Phayuth/delivery_robot/dlvr_resource/design/Part/Voltage_Display.SLDPRT

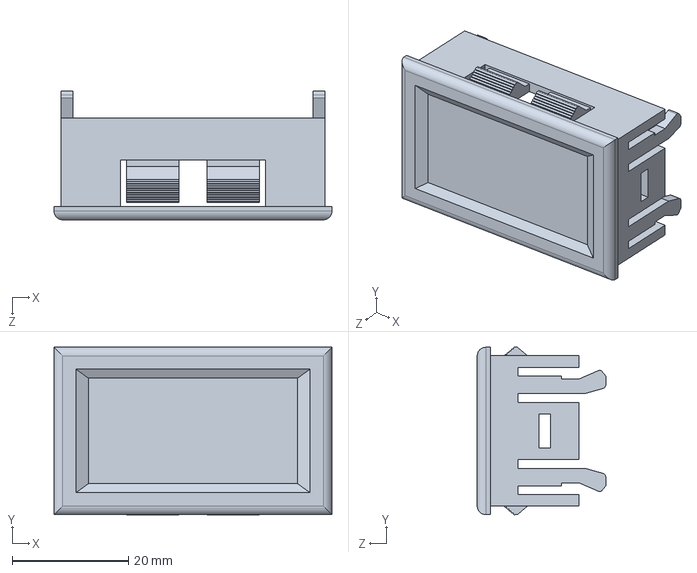
[picture p19: CAD file, 2022-11-23]
dlvr_resource/design/Part/Voltage_Display.SLDPRT
47.8 x 28.8 x 22.1 mm
