Phayuth/delivery_robot/dlvr_robot_description/meshes/laser_link.STL

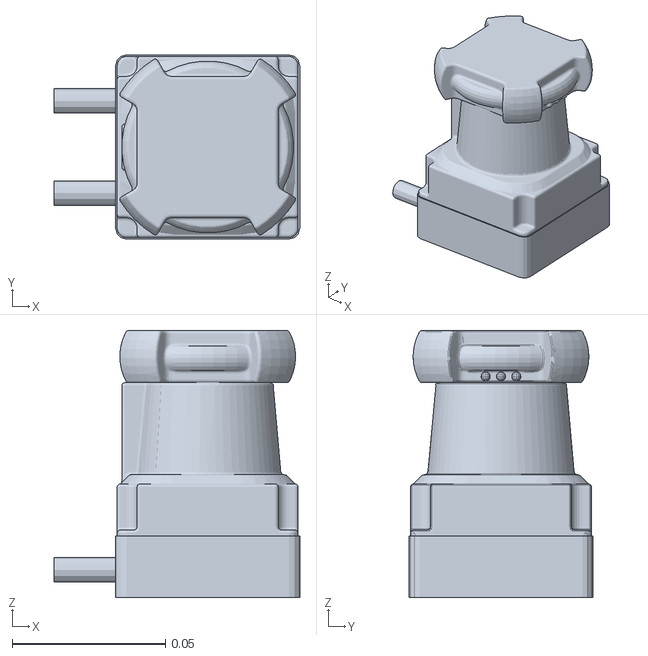
[picture p20: CAD file, 2022-11-23]
dlvr_robot_description/meshes/laser_link.STL
0.08 x 0.06 x 0.087
