Phayuth/delivery_robot/dlvr_resource/design/Part/Structure.SLDPRT

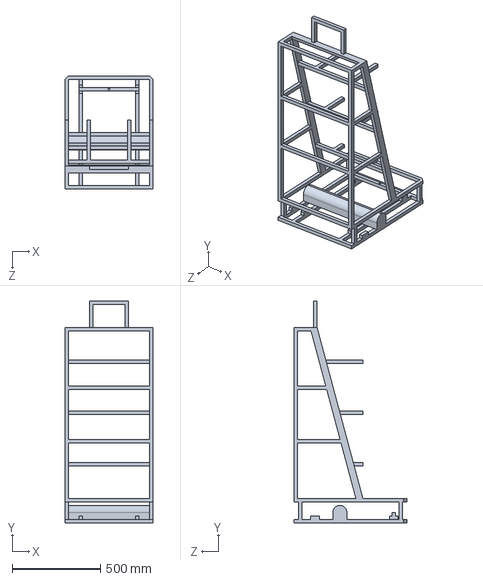
[picture p21: CAD file, 2022-11-23]
dlvr_resource/design/Part/Structure.SLDPRT
500.0 x 1255.9 x 640.0 mm
