Phayuth/delivery_robot/dlvr_resource/design/Part/Plate.SLDPRT

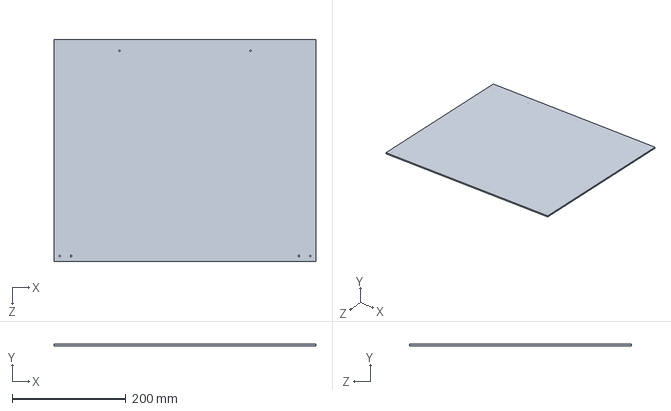
[picture p22: CAD file, 2022-11-23]
dlvr_resource/design/Part/Plate.SLDPRT
460.0 x 3.00 x 390.5 mm
