Phayuth/delivery_robot/dlvr_resource/design/Part/Top_Back_Cover_1.SLDPRT

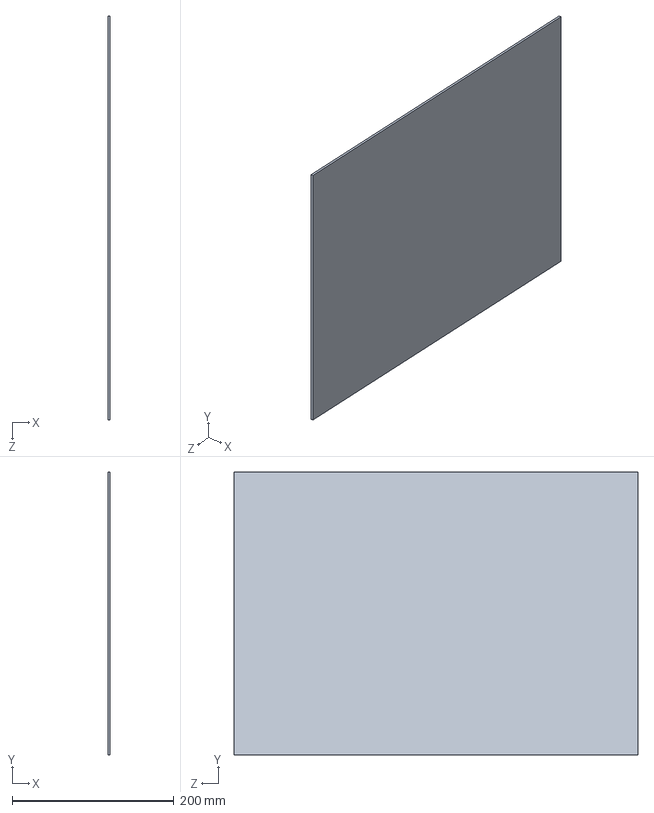
[picture p23: CAD file, 2022-11-23]
dlvr_resource/design/Part/Top_Back_Cover_1.SLDPRT
3.00 x 350.4 x 500.0 mm
