Phayuth/delivery_robot/dlvr_resource/design/Part/System_Controller_Support.SLDPRT

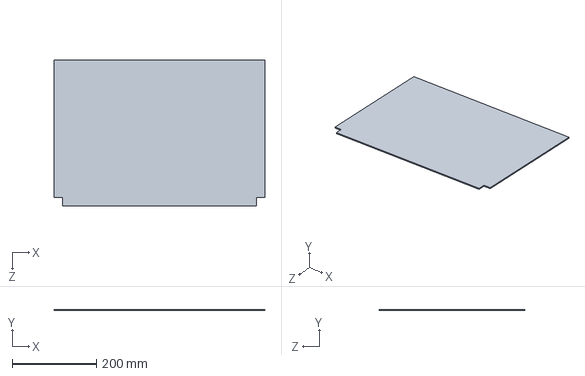
[picture p24: CAD file, 2022-11-23]
dlvr_resource/design/Part/System_Controller_Support.SLDPRT
500.0 x 3.00 x 345.0 mm
