Phayuth/delivery_robot/dlvr_resource/design/Part/Top_Side_Cover_2.SLDPRT

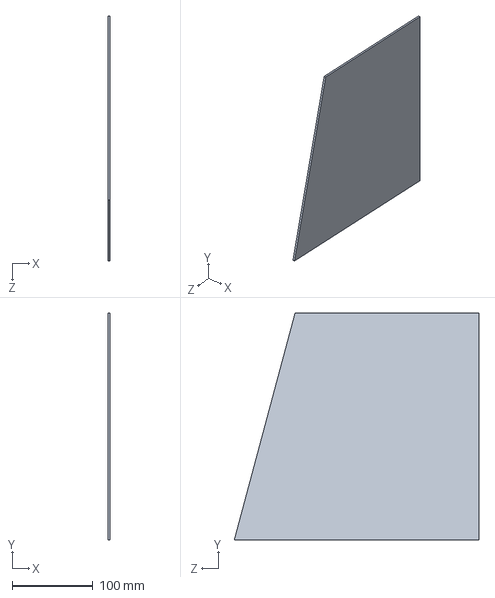
[picture p25: CAD file, 2022-11-23]
dlvr_resource/design/Part/Top_Side_Cover_2.SLDPRT
3.00 x 281.9 x 303.6 mm
