Phayuth/delivery_robot/dlvr_resource/design/Part/E_Stop_Button.SLDPRT

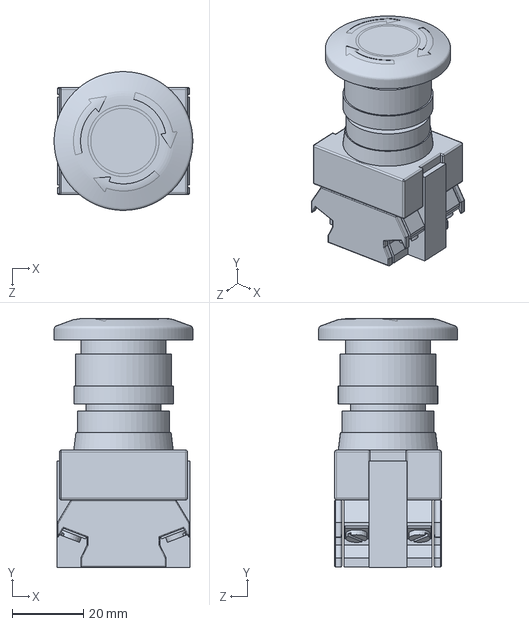
[picture p26: CAD file, 2022-11-23]
dlvr_resource/design/Part/E_Stop_Button.SLDPRT
39.0 x 70.0 x 39.0 mm
