Phayuth/delivery_robot/dlvr_resource/design/Part/Bottom_Angle_Cover_1.SLDPRT

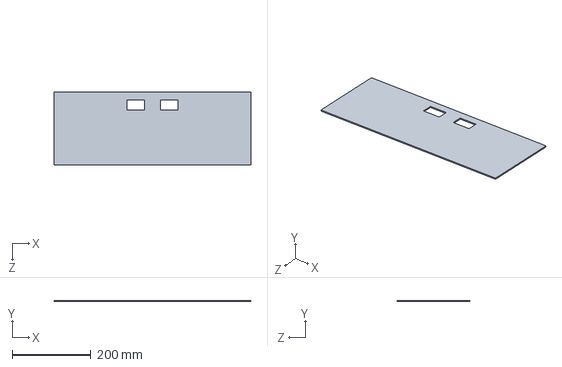
[picture p27: CAD file, 2022-11-23]
dlvr_resource/design/Part/Bottom_Angle_Cover_1.SLDPRT
500.0 x 3.00 x 185.0 mm
