Phayuth/delivery_robot/dlvr_resource/design/Part/AC_Power_Socket.SLDPRT

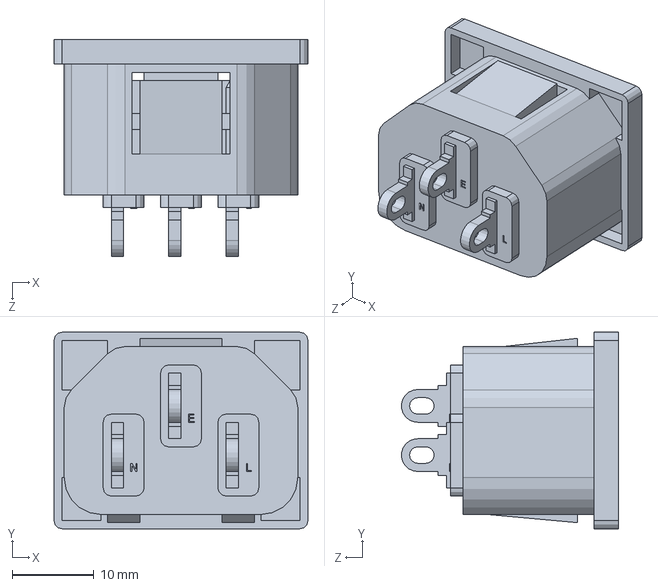
[picture p28: CAD file, 2022-11-23]
dlvr_resource/design/Part/AC_Power_Socket.SLDPRT
31.0 x 24.0 x 26.5 mm
