Phayuth/delivery_robot/dlvr_resource/design/Part/Bottom_Side_Cover.SLDPRT

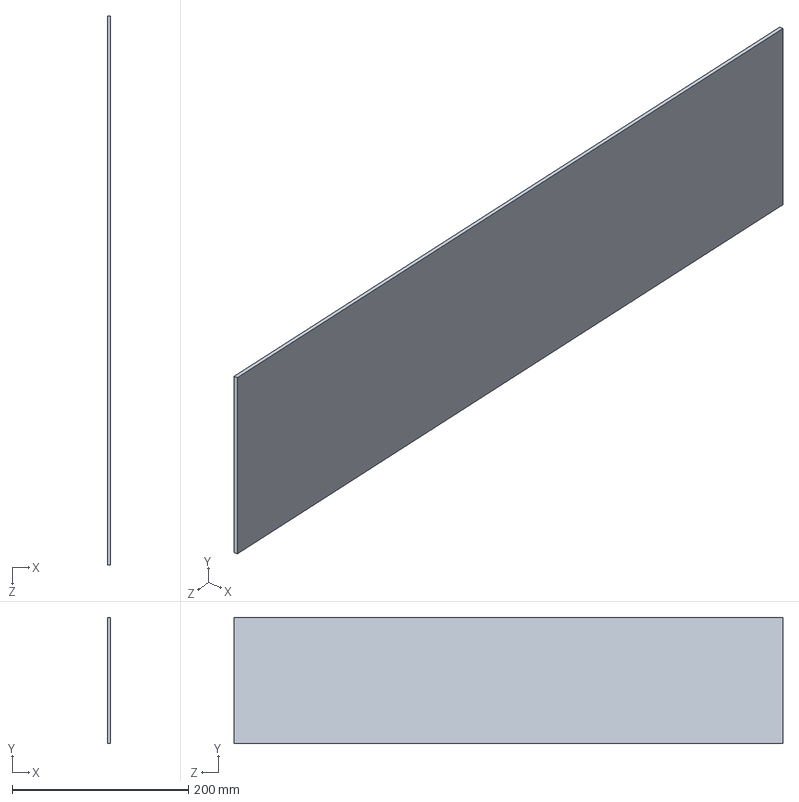
[picture p29: CAD file, 2022-11-23]
dlvr_resource/design/Part/Bottom_Side_Cover.SLDPRT
3.00 x 143.0 x 623.0 mm
