Phayuth/delivery_robot/dlvr_resource/design/Part/LCD_Support.SLDPRT

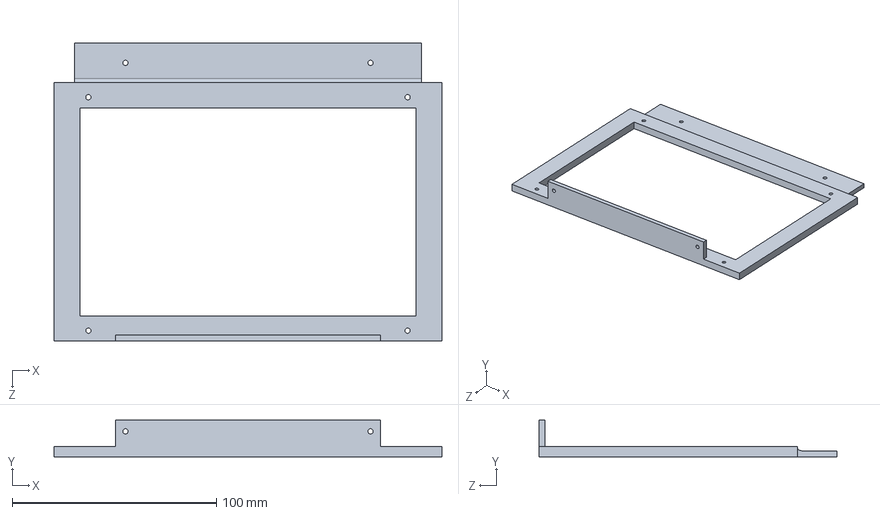
[picture p30: CAD file, 2022-11-23]
dlvr_resource/design/Part/LCD_Support.SLDPRT
190.0 x 18.0 x 146.0 mm
