Phayuth/delivery_robot/dlvr_resource/design/Part/Bottom_Front_Cover.SLDPRT

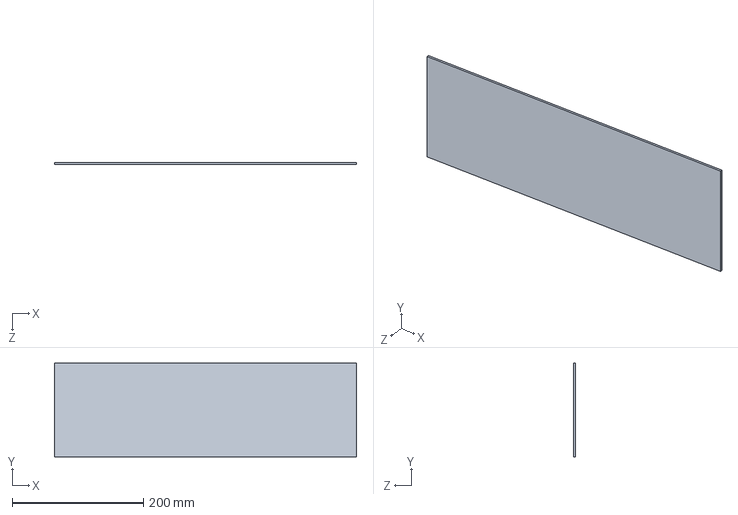
[picture p31: CAD file, 2022-11-23]
dlvr_resource/design/Part/Bottom_Front_Cover.SLDPRT
460.0 x 143.0 x 3.00 mm
