Phayuth/delivery_robot/dlvr_resource/design/Part/Logitech_C920.SLDPRT

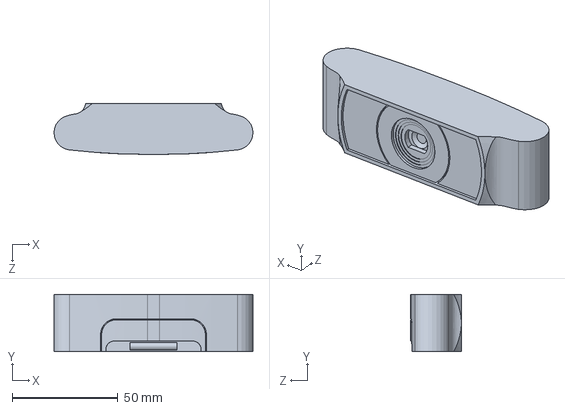
[picture p32: CAD file, 2022-11-23]
dlvr_resource/design/Part/Logitech_C920.SLDPRT
94.0 x 27.0 x 24.0 mm
