Phayuth/delivery_robot/dlvr_resource/design/Part/Top_Top_Cover.SLDPRT

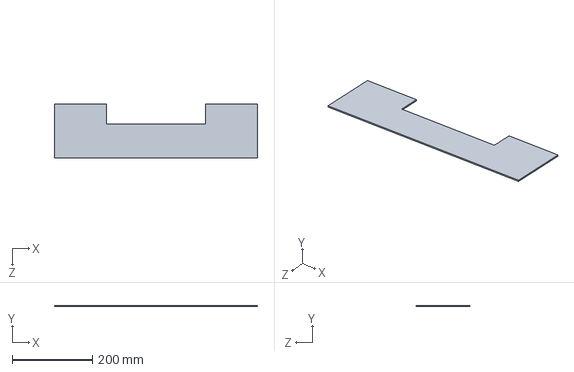
[picture p33: CAD file, 2022-11-23]
dlvr_resource/design/Part/Top_Top_Cover.SLDPRT
506.0 x 3.00 x 134.2 mm
