Phayuth/delivery_robot/dlvr_resource/design/Part/System_Monitor_Support.SLDPRT

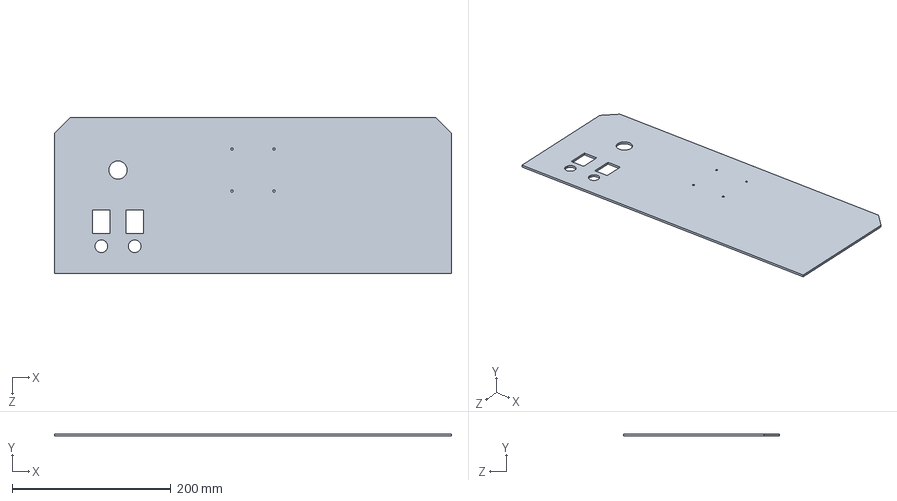
[picture p34: CAD file, 2022-11-23]
dlvr_resource/design/Part/System_Monitor_Support.SLDPRT
500.0 x 3.00 x 197.1 mm
