Phayuth/delivery_robot/dlvr_resource/design/Part/LIDAR_Hokuyo_UTM_30LX.SLDPRT

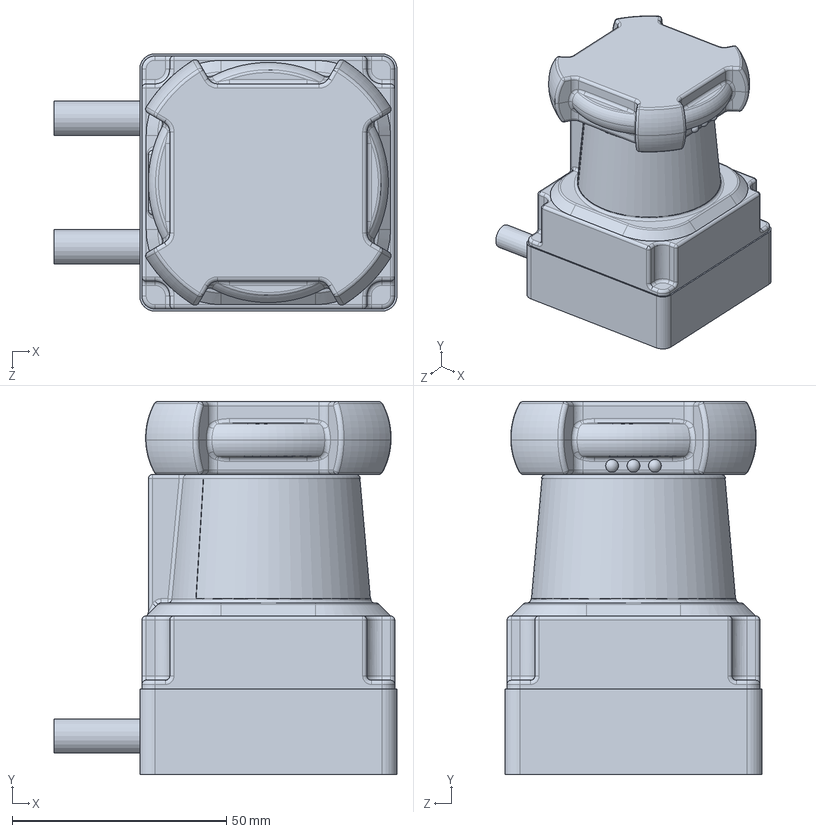
[picture p36: CAD file, 2022-11-23]
dlvr_resource/design/Part/LIDAR_Hokuyo_UTM_30LX.SLDPRT
80.0 x 87.0 x 60.0 mm
