Phayuth/delivery_robot/dlvr_resource/design/Part/Bottom_Chamfer_Cover.SLDPRT

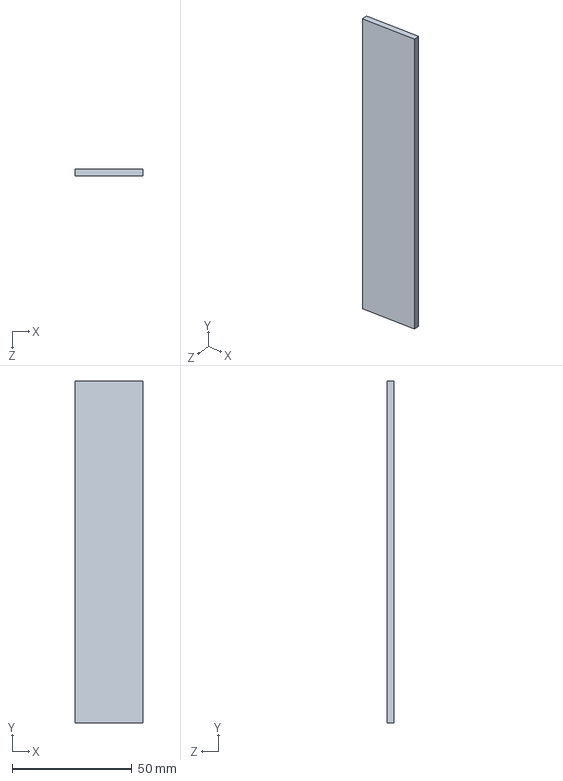
[picture p37: CAD file, 2022-11-23]
dlvr_resource/design/Part/Bottom_Chamfer_Cover.SLDPRT
28.3 x 143.0 x 3.00 mm
