Phayuth/delivery_robot/dlvr_resource/design/Part/Battery_Switch.SLDPRT

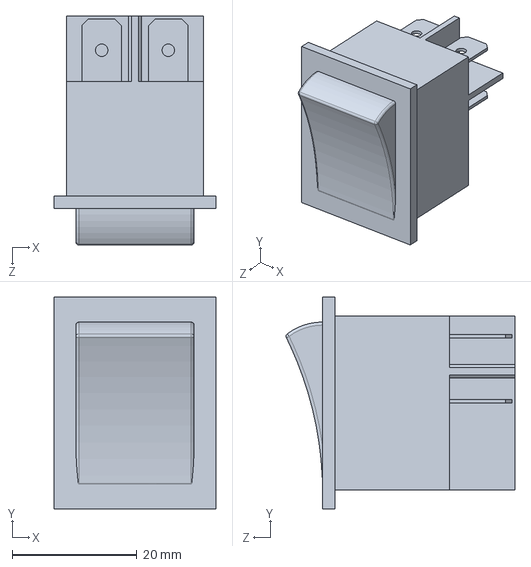
[picture p38: CAD file, 2022-11-23]
dlvr_resource/design/Part/Battery_Switch.SLDPRT
26.0 x 34.0 x 36.8 mm
