Phayuth/delivery_robot/dlvr_resource/design/Part/Bottom_Battery_Support_2.SLDPRT

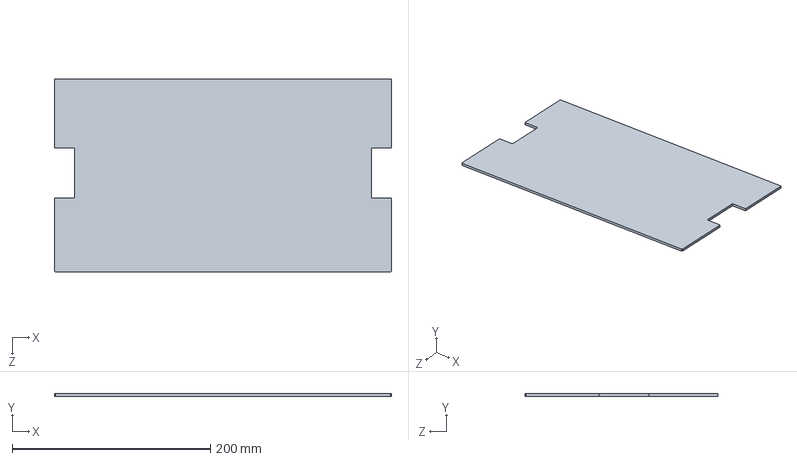
[picture p39: CAD file, 2022-11-23]
dlvr_resource/design/Part/Bottom_Battery_Support_2.SLDPRT
340.0 x 3.00 x 195.0 mm
