Phayuth/delivery_robot/dlvr_resource/design/Part/Bottom_Back_Cover.SLDPRT

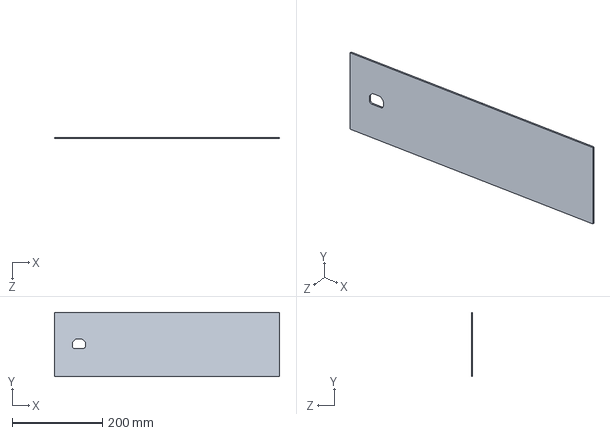
[picture p41: CAD file, 2022-11-23]
dlvr_resource/design/Part/Bottom_Back_Cover.SLDPRT
500.0 x 143.0 x 3.00 mm
