Phayuth/delivery_robot/dlvr_resource/design/Part/Top_Side_Cover_3.SLDPRT

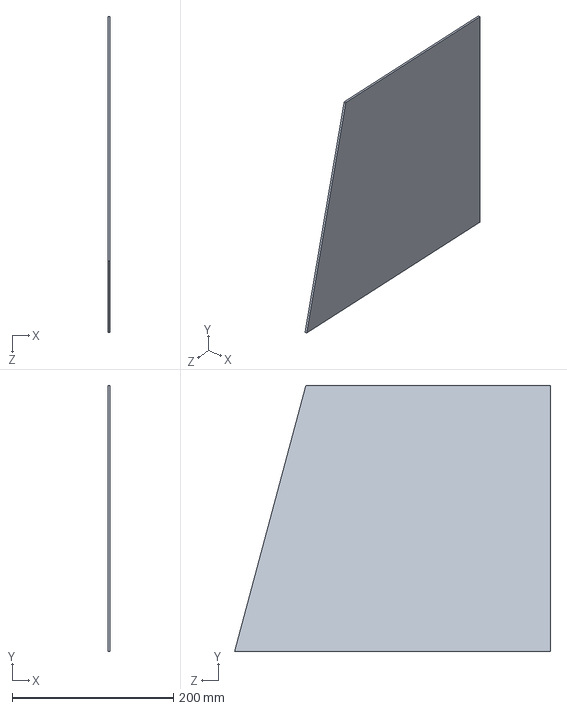
[picture p42: CAD file, 2022-11-23]
dlvr_resource/design/Part/Top_Side_Cover_3.SLDPRT
3.00 x 330.7 x 392.2 mm
