Phayuth/delivery_robot/dlvr_resource/design/Part/Bottom_Angle_Cover_2.SLDPRT

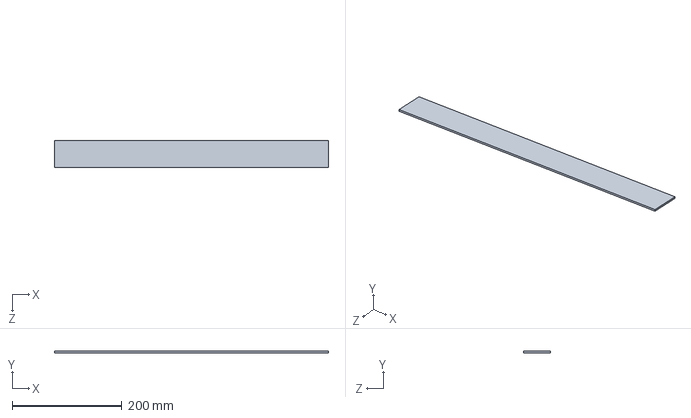
[picture p43: CAD file, 2022-11-23]
dlvr_resource/design/Part/Bottom_Angle_Cover_2.SLDPRT
500.0 x 3.00 x 50.0 mm
