Phayuth/delivery_robot/dlvr_resource/dlvr_oldsrc/Arduino/arduino_code_v3/encoder.ino

void ai10() {
  if (digitalRead(enc_left_A) == HIGH) {
    if (digitalRead(enc_left_B) == LOW) {
      counter_left--;
    }
    else {
      counter_left++;
    }
  }
  else {
    if (digitalRead(enc_left_B) == LOW) {
      counter_left++;
    }
    else {
      counter_left--;
    }
  }
  left_wheel_tick_count.data = counter_left;
}

void ai11() {
  if (digitalRead(enc_left_B) == HIGH) {
    if (digitalRead(enc_left_A) == LOW) {
      counter_left++;
    }
    else {
      counter_left--;
    }
  }
  else {
    if (digitalRead(enc_left_A) == LOW) {
      counter_left--;
    }
    else {
      counter_left++;
    }
  }
  left_wheel_tick_count.data = counter_left;
}


void ai8() {
  if (digitalRead(enc_right_A) == HIGH) {
    if (digitalRead(enc_right_B) == LOW) {
      counter_right++;
    }
    else {
      counter_right--;
    }
  }
  else {
    if (digitalRead(enc_right_B) == LOW) {
      counter_right--;
    }
    else {
      counter_right++;
    }
  }
  right_wheel_tick_count.data = counter_right;
}

void ai9() {
  if (digitalRead(enc_right_B) == HIGH) {
    if (digitalRead(enc_right_A) == LOW) {
      counter_right--;
    }
    else {
      counter_right++;
    }
  }
  else {
    if (digitalRead(enc_right_A) == LOW) {
      counter_right++;
    }
    else {
      counter_right--;
    }
  }
  right_wheel_tick_count.data = counter_right;
}
